devfabiosilva/TeslaSMPS/04-hand-made-prototype/01-Begin/CAM01209.jpg

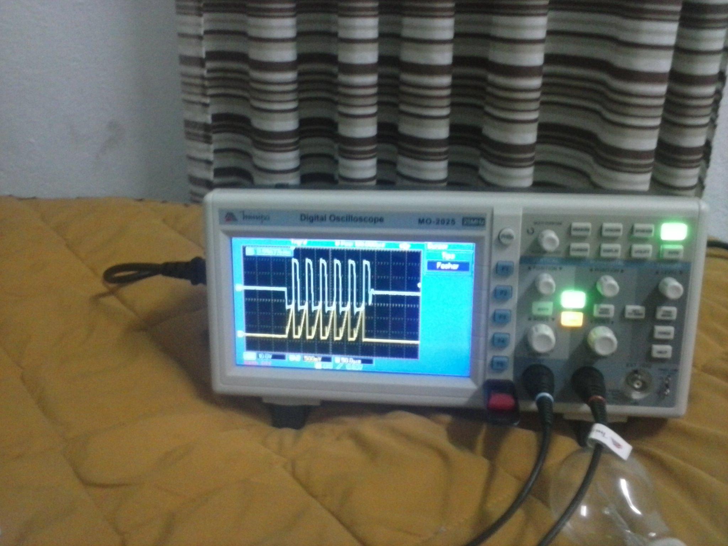
04-hand-made-prototype/01-Begin/CAM01209.jpg
