devfabiosilva/TeslaSMPS/04-hand-made-prototype/01-Begin/CAM01234.jpg

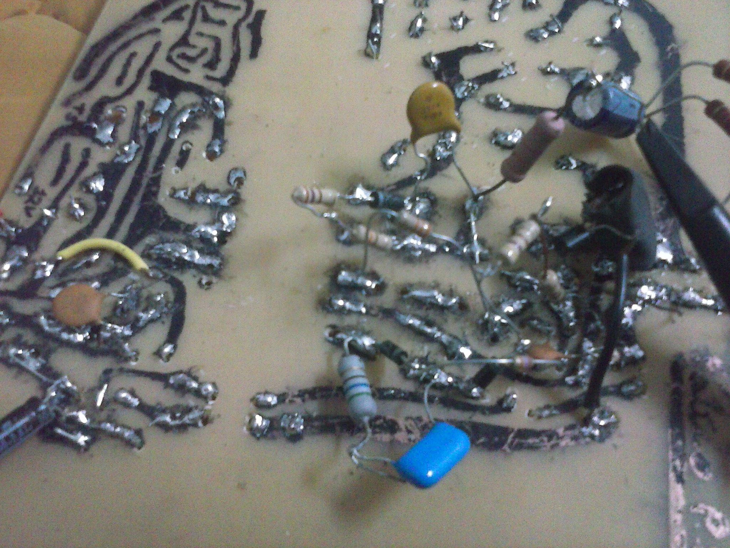
04-hand-made-prototype/01-Begin/CAM01234.jpg
