devfabiosilva/TeslaSMPS/04-hand-made-prototype/01-Begin/CAM01353.jpg

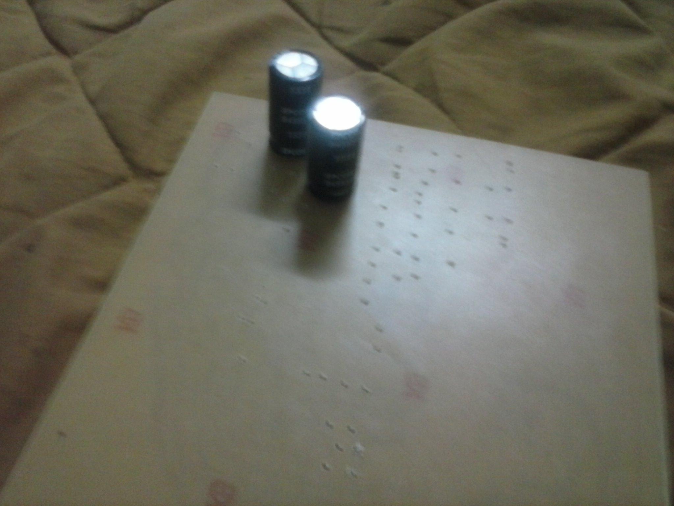
04-hand-made-prototype/01-Begin/CAM01353.jpg
