devfabiosilva/TeslaSMPS/04-hand-made-prototype/01-Begin/CAM01364.jpg

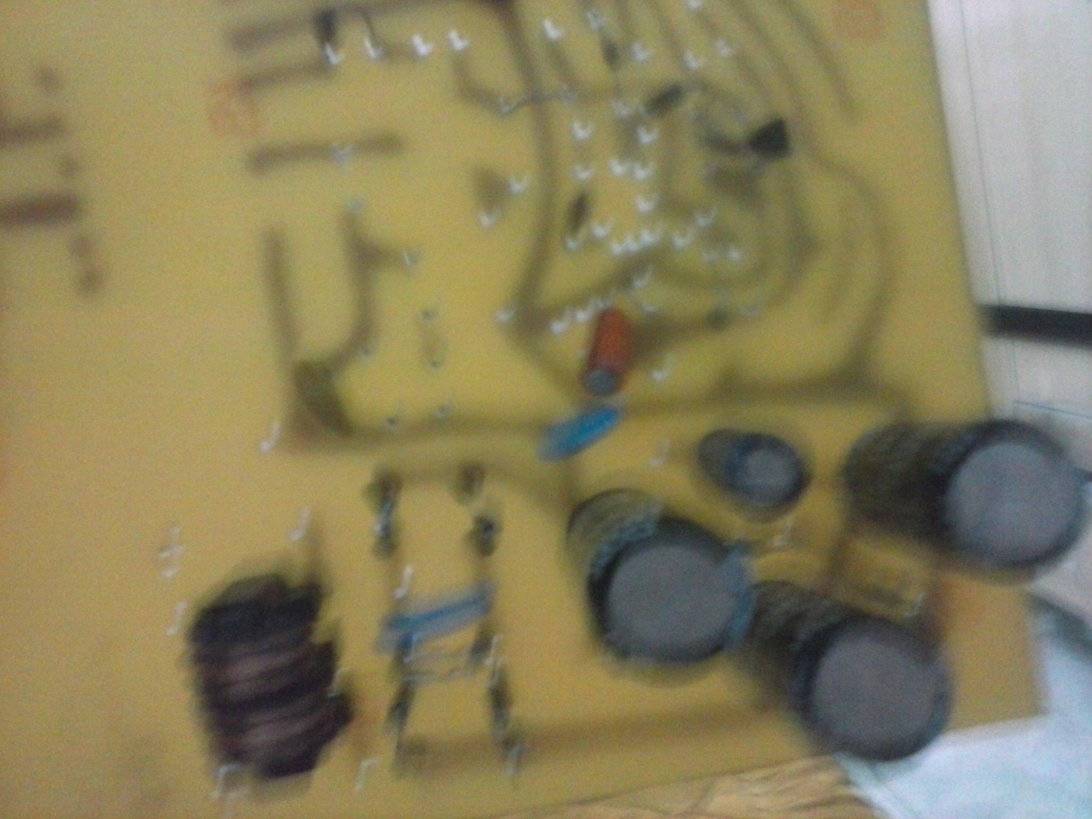
04-hand-made-prototype/01-Begin/CAM01364.jpg
