devfabiosilva/TeslaSMPS/04-hand-made-prototype/01-Begin/CAM01391.jpg

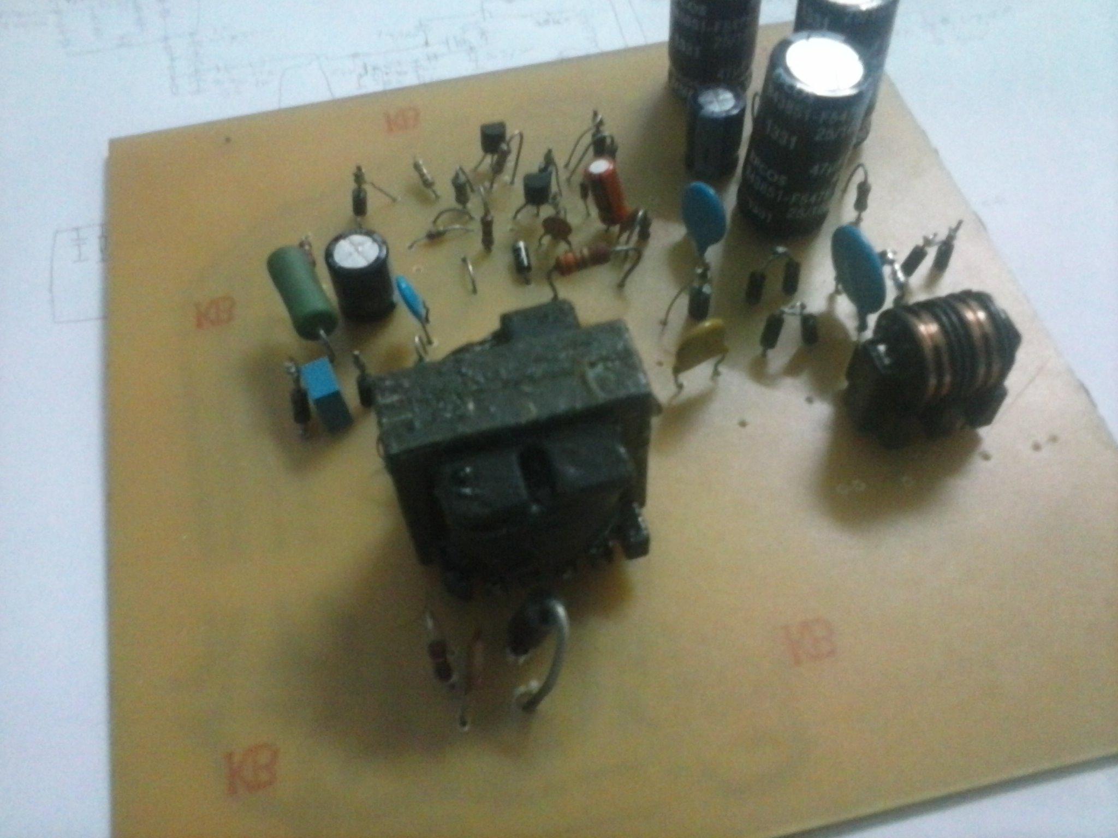
04-hand-made-prototype/01-Begin/CAM01391.jpg
