devfabiosilva/TeslaSMPS/04-hand-made-prototype/02-Final/20160407_155806.jpg

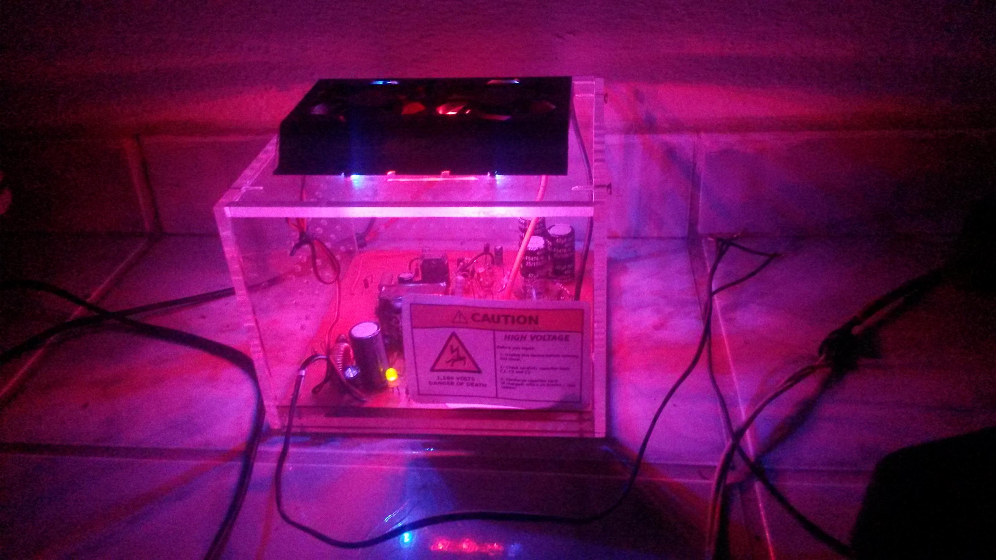
04-hand-made-prototype/02-Final/20160407_155806.jpg
