devfabiosilva/TeslaSMPS/04-hand-made-prototype/02-Final/20190126_161324.jpg

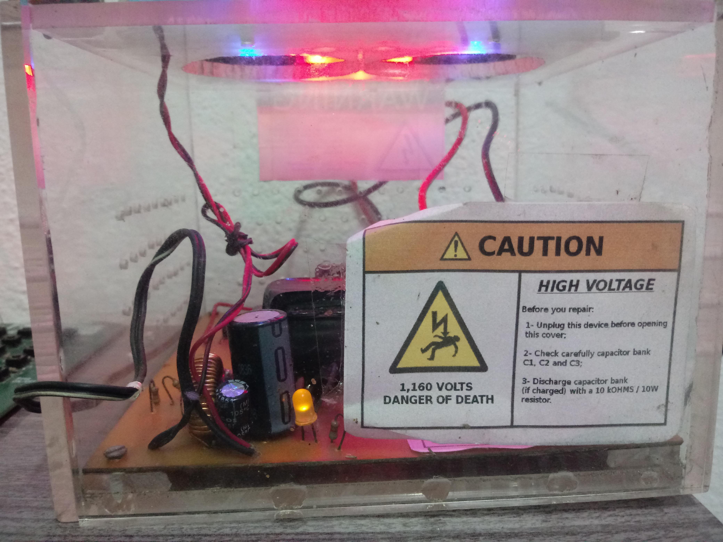
04-hand-made-prototype/02-Final/20190126_161324.jpg
